mpinese/scalable_field_camera/STL_4x5/back_plate_structural.stl

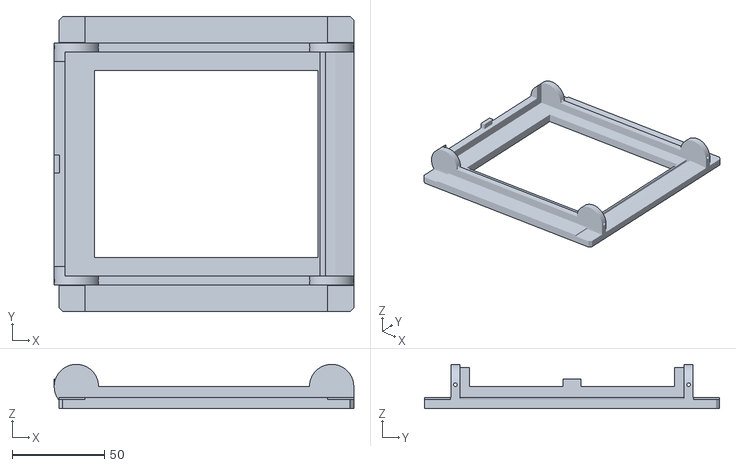
[picture p15: CAD file, 2026-02-03]
STL_4x5/back_plate_structural.stl
162.1 x 159.6 x 24.0
