mpinese/scalable_field_camera/STL_4x5/lensboard_upper_clamp_control.stl

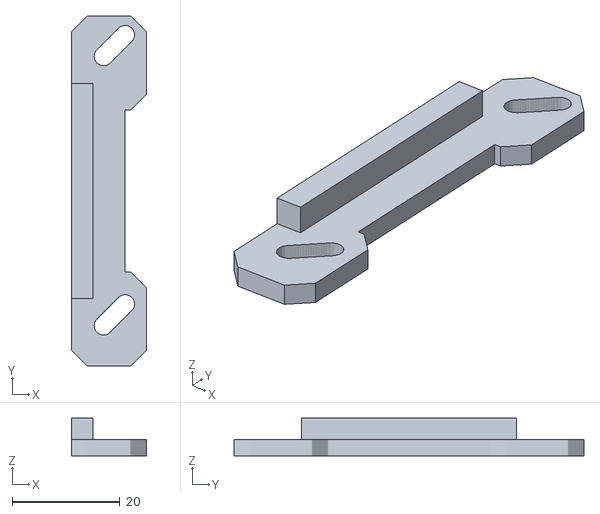
[picture p16: CAD file, 2026-02-03]
STL_4x5/lensboard_upper_clamp_control.stl
14.0 x 65.0 x 7.00
