mpinese/scalable_field_camera/STL_4x5/pulling_lever_control.stl

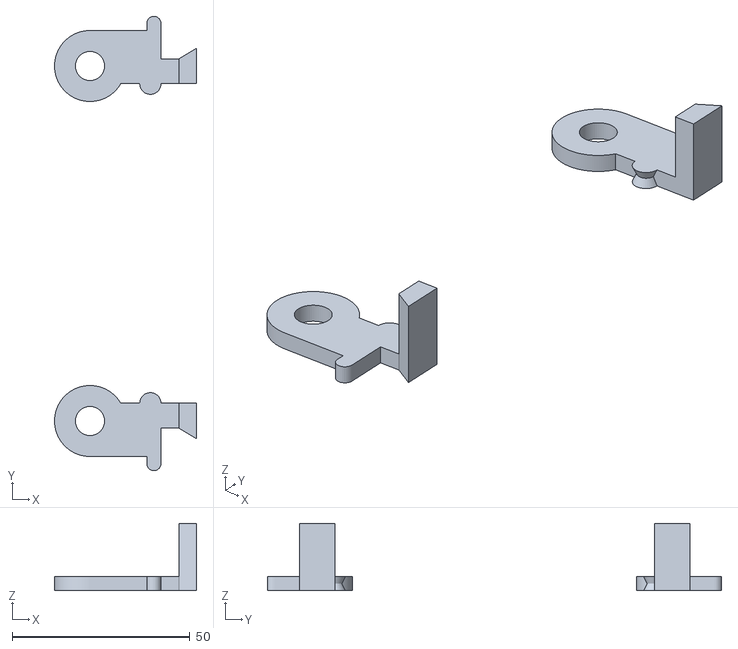
[picture p17: CAD file, 2026-02-03]
STL_4x5/pulling_lever_control.stl
40.0 x 128.0 x 19.0
