mpinese/scalable_field_camera/STL_4x5/front_lid_dovetail_structural.stl

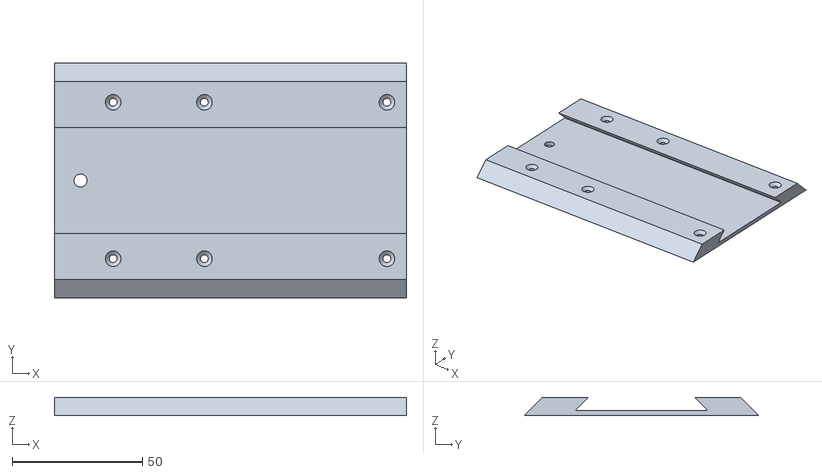
[picture p18: CAD file, 2026-02-03]
STL_4x5/front_lid_dovetail_structural.stl
135.0 x 90.0 x 7.00
