mpinese/scalable_field_camera/STL_4x5/slider_structural.stl

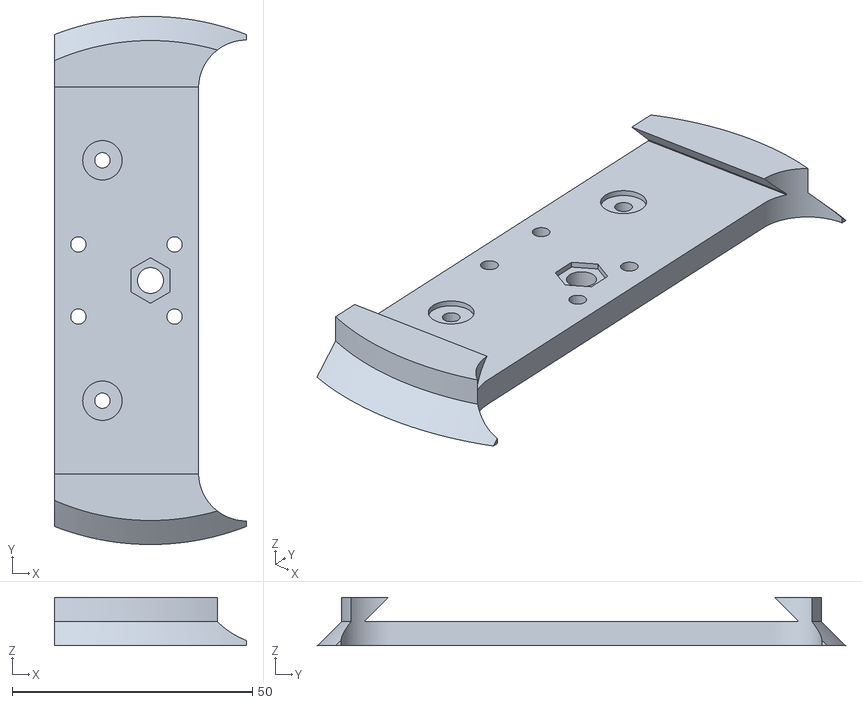
[picture p19: CAD file, 2026-02-03]
STL_4x5/slider_structural.stl
40.0 x 109.8 x 10.0
