mpinese/scalable_field_camera/STL_4x5/ground_glass_clamp_general.stl

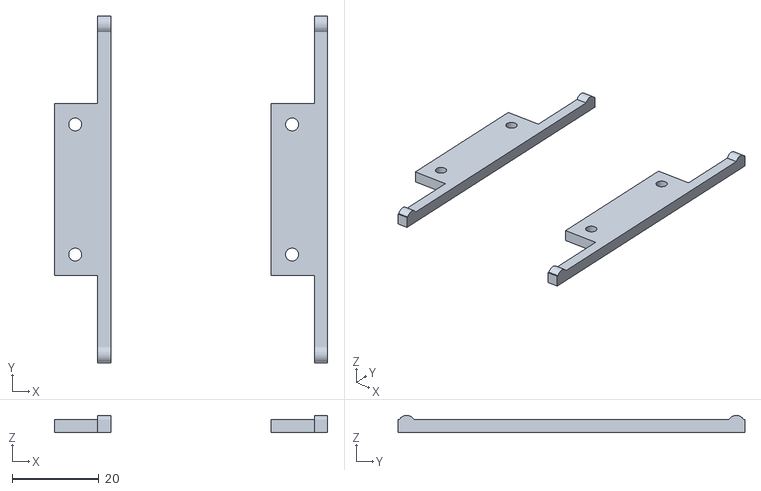
[picture p20: CAD file, 2026-02-03]
STL_4x5/ground_glass_clamp_general.stl
63.0 x 80.0 x 4.00
