mpinese/scalable_field_camera/STL_4x5/front_lid_structural.stl

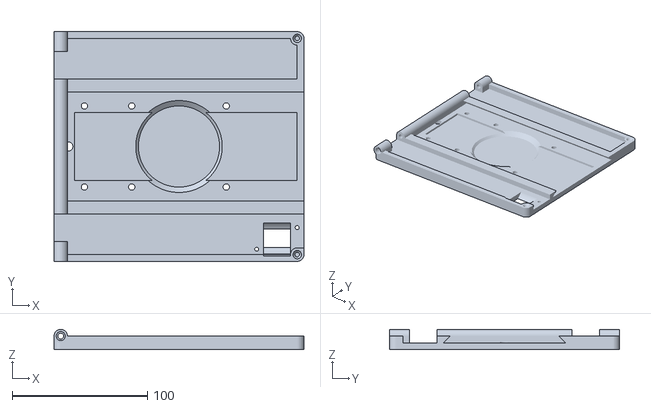
[picture p21: CAD file, 2026-02-03]
STL_4x5/front_lid_structural.stl
185.0 x 170.0 x 15.0
