mpinese/scalable_field_camera/STL_4x5/rails_structural.stl

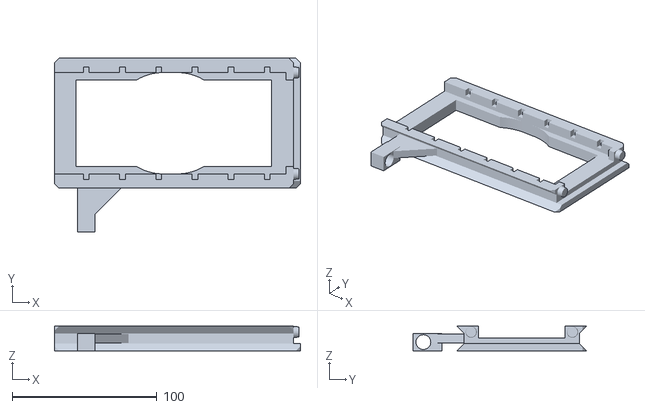
[picture p22: CAD file, 2026-02-03]
STL_4x5/rails_structural.stl
170.0 x 119.9 x 17.0
