mpinese/scalable_field_camera/STL_4x5/tripod_plate_structural.stl

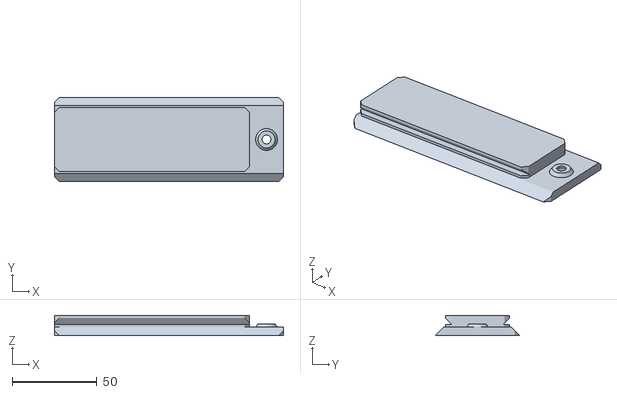
[picture p23: CAD file, 2026-02-03]
STL_4x5/tripod_plate_structural.stl
135.0 x 49.8 x 12.0
