mpinese/scalable_field_camera/STL_4x5/body_structural.stl

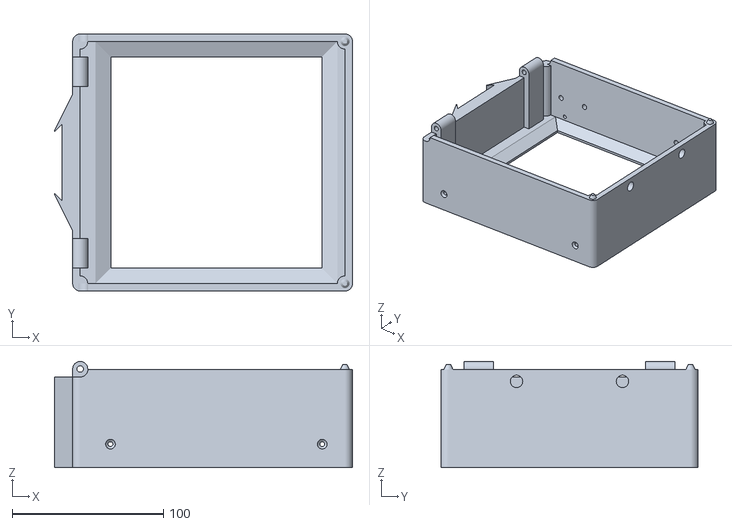
[picture p24: CAD file, 2026-02-03]
STL_4x5/body_structural.stl
197.0 x 170.0 x 70.2
