mpinese/scalable_field_camera/STL_4x5/front_standard_tilt_plate_structural.stl

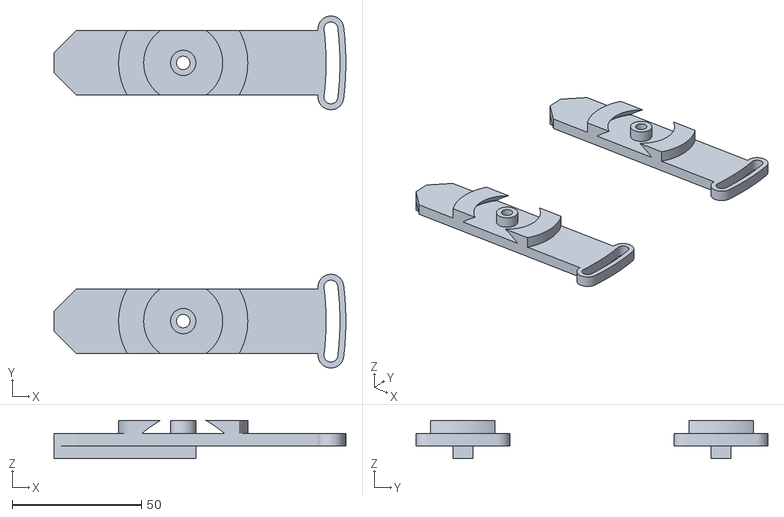
[picture p25: CAD file, 2026-02-03]
STL_4x5/front_standard_tilt_plate_structural.stl
113.0 x 136.3 x 14.8
